solarmon/RGBtoHDMI-CDTV/RGBtoHDMI Amiga Denise CPLD FFC - CDTV Video Slot/Installation/RGBtoHDMI CDTV - Installation - Denise Break and Flex Cable - Side.JPG

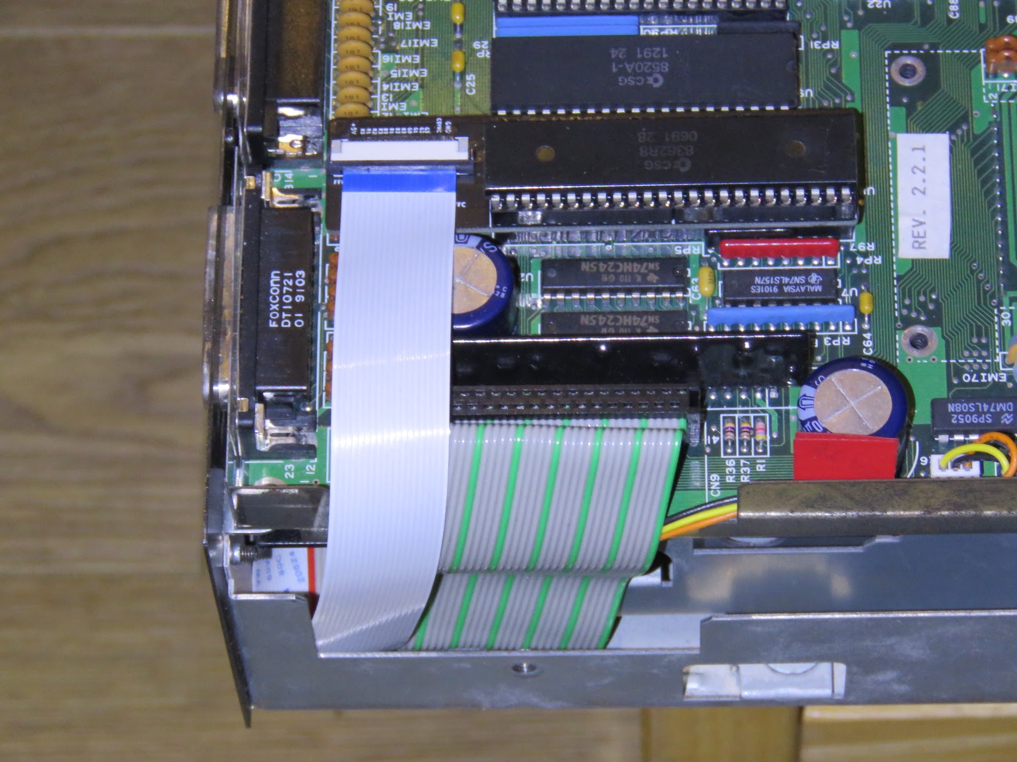
RGBtoHDMI Amiga Denise CPLD FFC - CDTV Video Slot/Installation/RGBtoHDMI CDTV - Installation - Denise Break and Flex Cable - Side.JPG
