solarmon/RGBtoHDMI-CDTV/RGBtoHDMI Amiga Denise CPLD FFC - CDTV Video Slot/Installation/RGBtoHDMI CDTV - Installation - Main Board Flex Cable.JPG

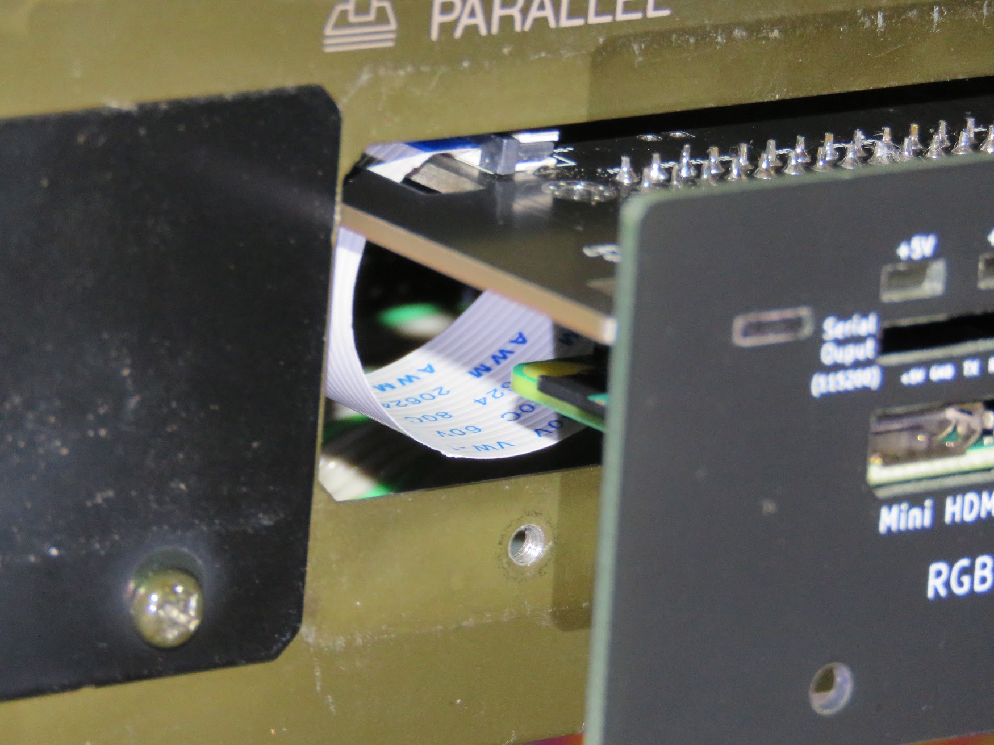
RGBtoHDMI Amiga Denise CPLD FFC - CDTV Video Slot/Installation/RGBtoHDMI CDTV - Installation - Main Board Flex Cable.JPG
