solarmon/RGBtoHDMI-CDTV/RGBtoHDMI Amiga Denise CPLD FFC - CDTV Video Slot/Installation/RGBtoHDMI CDTV - LED - Both Installed.jpg

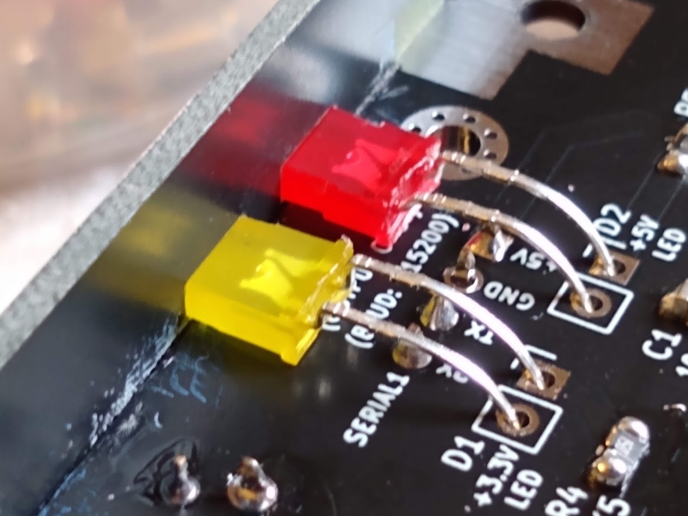
RGBtoHDMI Amiga Denise CPLD FFC - CDTV Video Slot/Installation/RGBtoHDMI CDTV - LED - Both Installed.jpg
