solarmon/RGBtoHDMI-CDTV/RGBtoHDMI Amiga Denise CPLD FFC - CDTV Video Slot/RGBtoHDMI-CDTV-Quick-Start-Guide.png

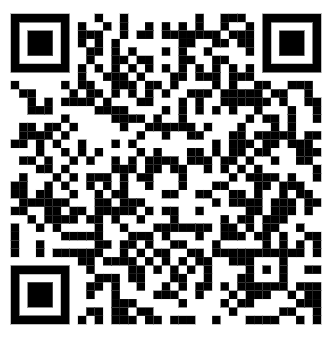
RGBtoHDMI Amiga Denise CPLD FFC - CDTV Video Slot/RGBtoHDMI-CDTV-Quick-Start-Guide.png
